fherbine/Electronic_project/TP/Altium/PCB_Project_TP/TP_Files/AssemblyDrawing.PDF

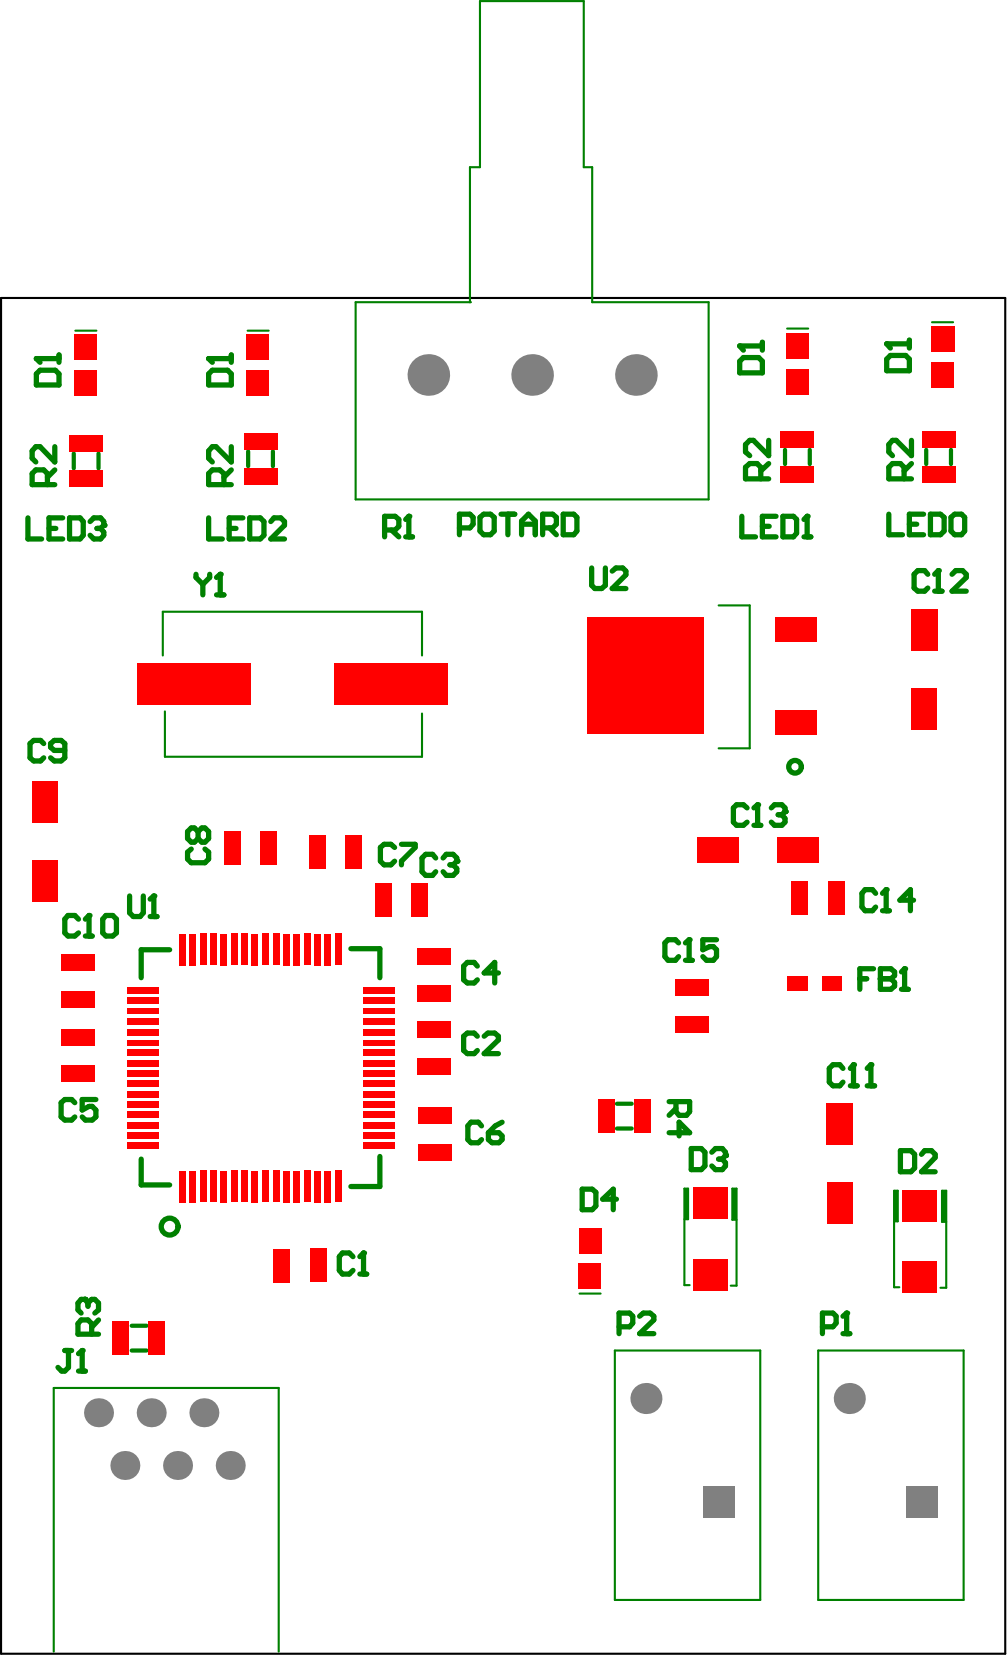
[picture p93: page 1]
