fherbine/Electronic_project/TP/Altium/PCB_Project_TP/TP_Files/MechanicalsDrawings.pdf

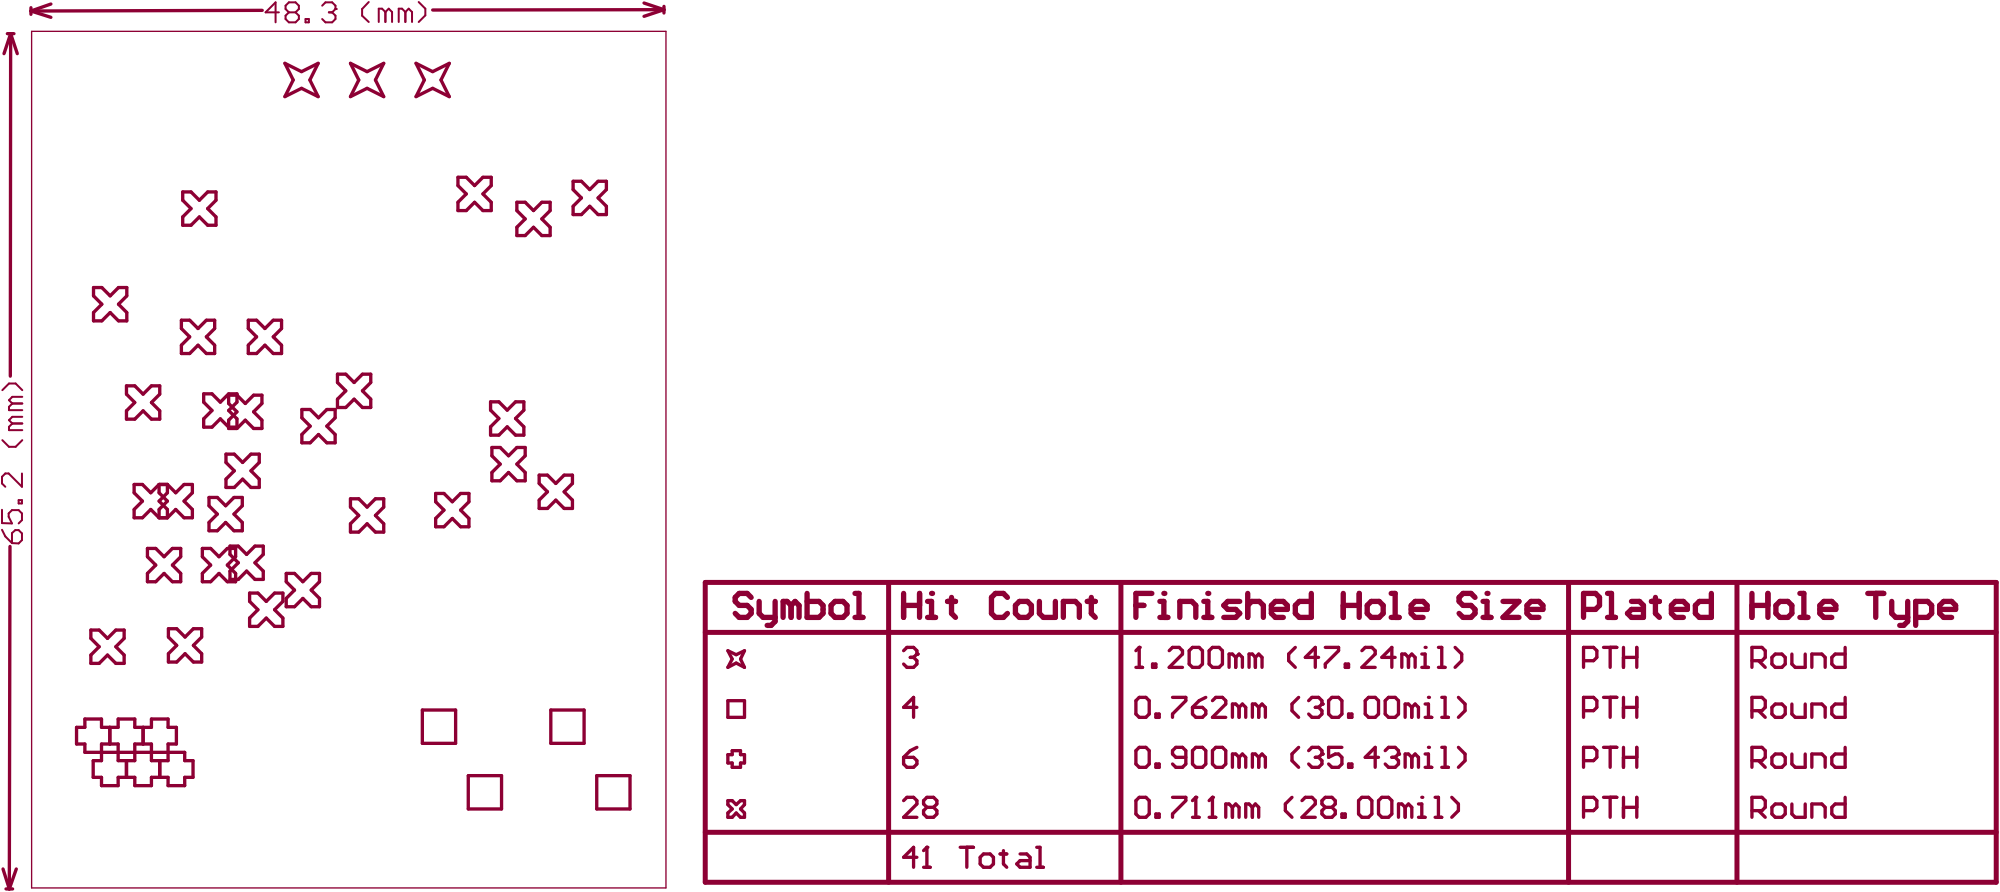
[picture p94: page 1]

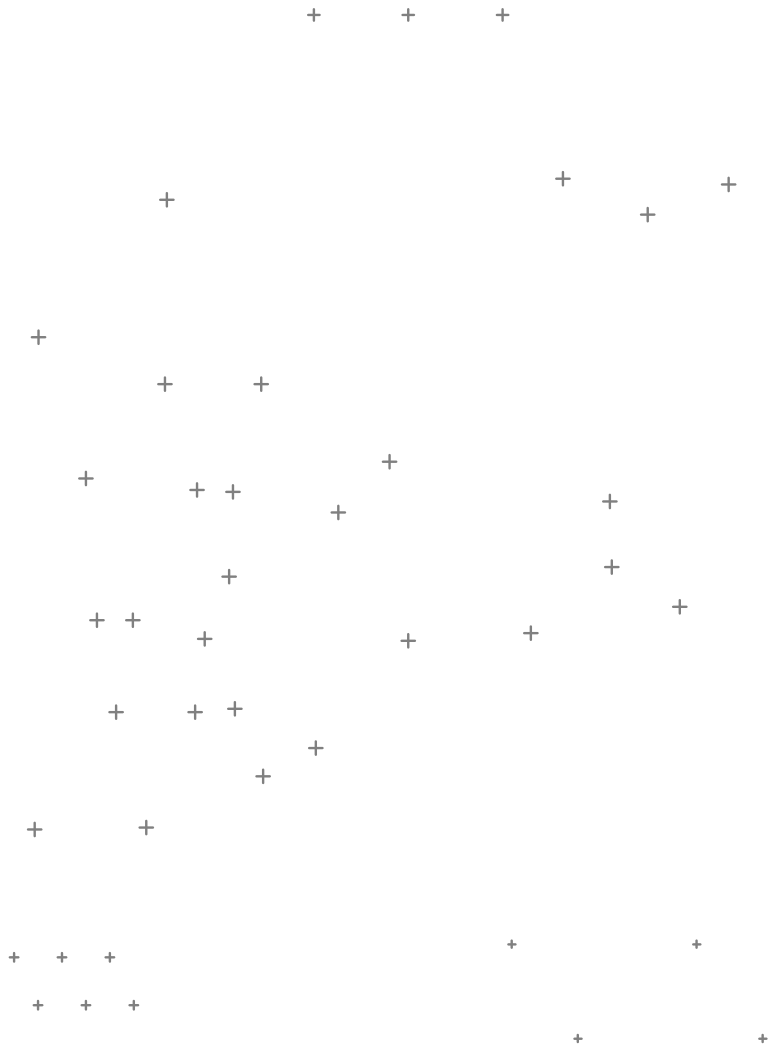
[picture p95: page 2]
