fherbine/Electronic_project/TP/Altium/PCB_Project_TP/TP_Files/Schmatics.PDF

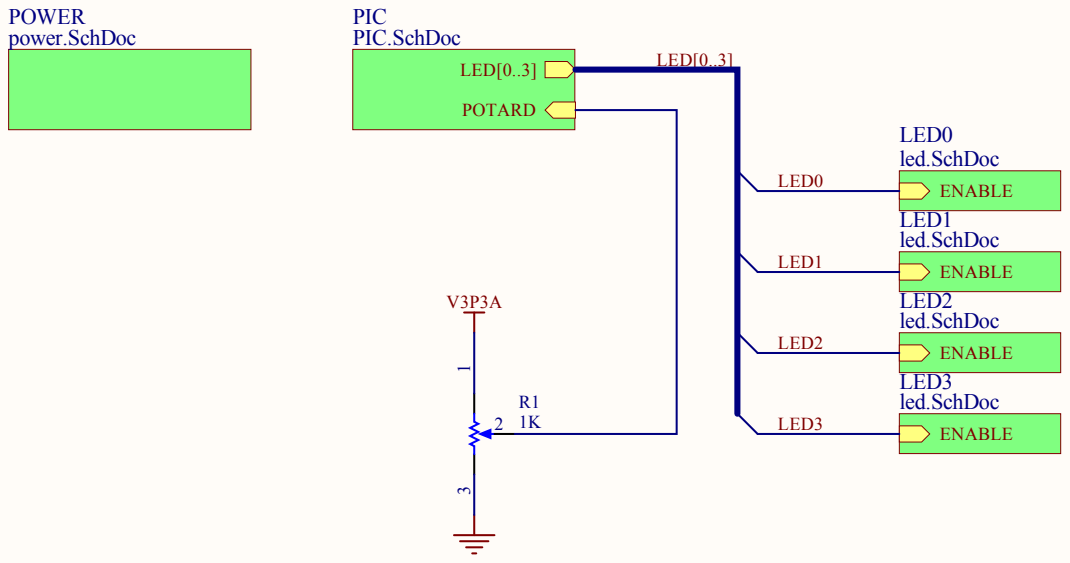
[picture p96: page 1]

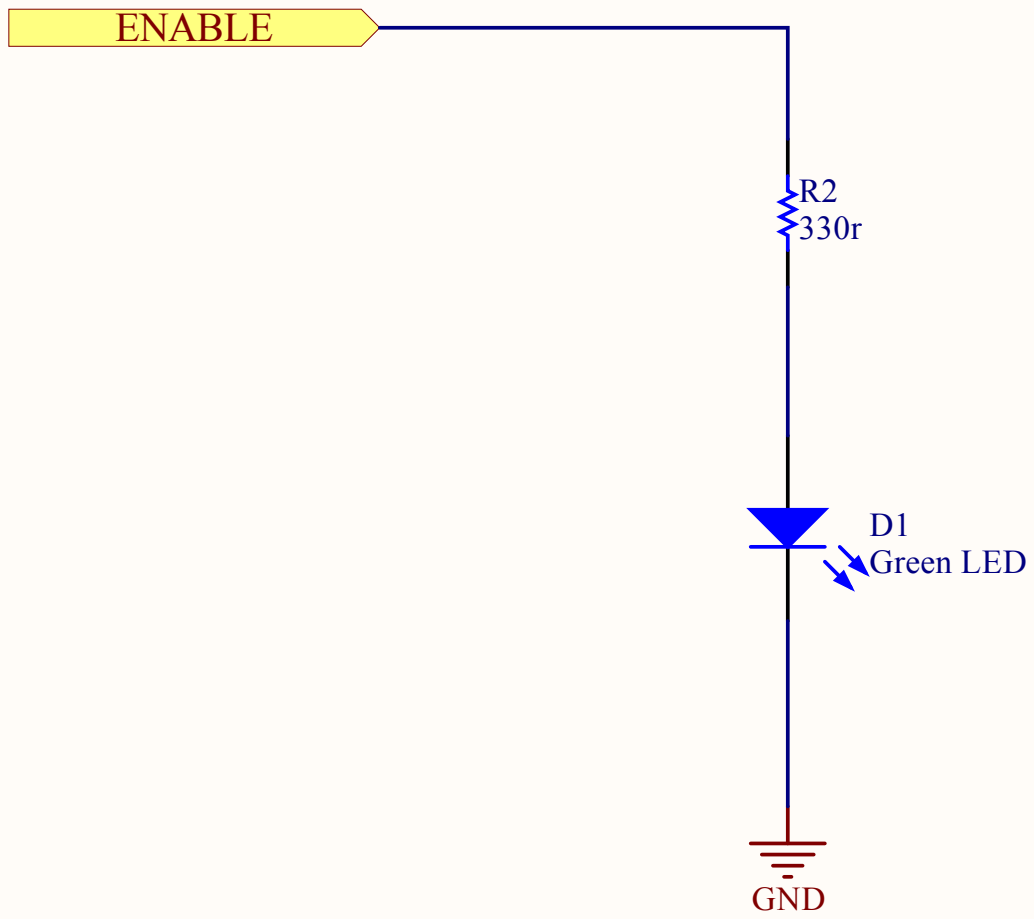
[picture p97: page 2]

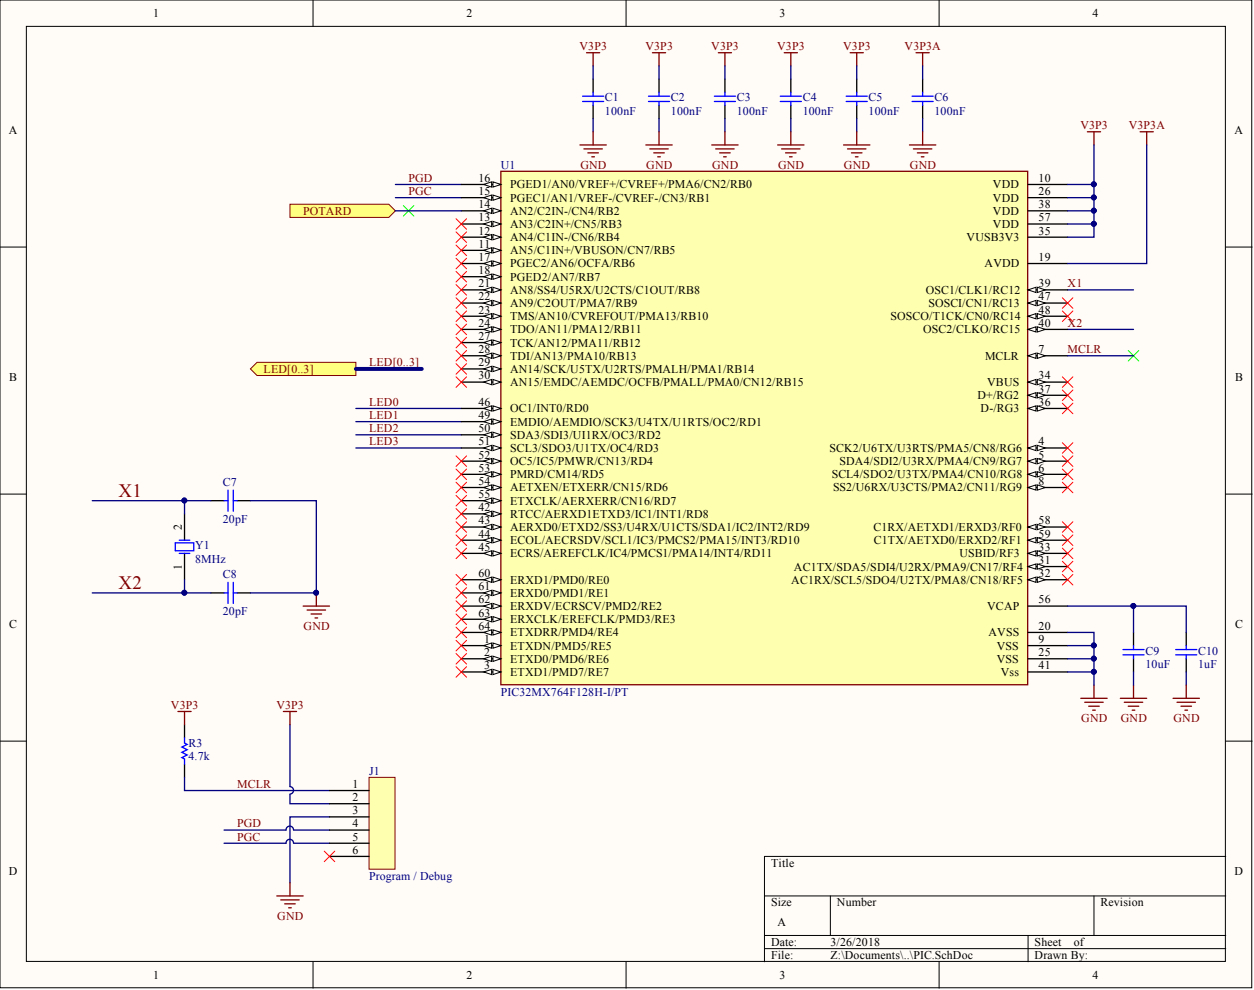
[picture p98: page 3]

2 6
3 8
5 7
3 5

2 0

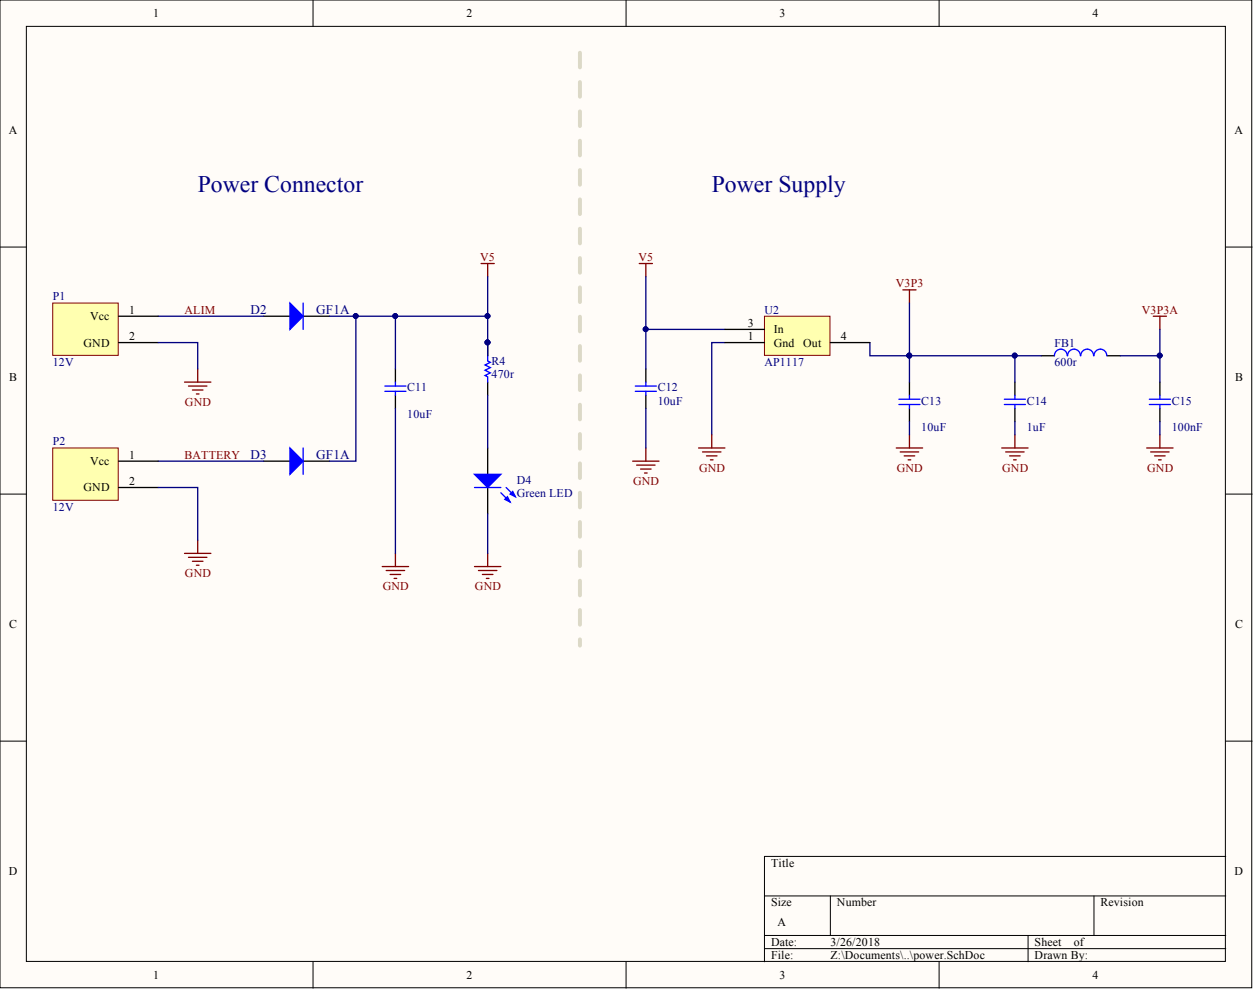
[picture p99: page 4]
