fherbine/Electronic_project/firmware/CompassIO/CompassIO_final/sources/communications.c

#include "types.h"

double parse_float(char *data, unsigned int size)
{
	long long offset = 1;
	long long floatValue = 1;
	long long result = 0;
	short neg = 1;
	int i = size;
	while (i)
	{
		if (i - 1 == 0 && data[0] == '-')
		{
			neg = -1;
			break;
		}
		if (data[i - 1] != '.' && data[i - 1] != '-')
		{
			result += (data[i - 1] - '0') * offset;
			offset *= 10;
		} else if (data[i - 1] == '.')
			floatValue = offset;
		else if (data[i - 1] < '0' && data[i - 1] > '9') // Handle wrong format
			return (999.999);
		i--;
	}
	return (((double)result/(double)floatValue) * (double)neg);
}

// lat xx.xxxxxx;long xxx.xxxxxx
u8 parser_gps_bluetooth(char *data, struct s_data *data_s)
{
	double lat = 0.0;
	double lon = 0.0;
	int separatorIndex = ft_index(data, ';');
	if (separatorIndex >= 0) {
		if (!ft_strncmp(data, "lat ", 4))
		{
			data += 4;
			lat = parse_float(data, separatorIndex - 4);
			if (lat < -90.0 || lat > 90.0) {
				//ft_putendl("Wrong latitude data");
				data_s->dest_coord.completed = FALSE;
				return (-1);
			}
			data += separatorIndex - 4 + 1; // - "lat " (4) + ";" (1)
			if (!ft_strncmp(data, "long ", 5))
			{
				data += 5;
				lon = parse_float(data, ft_strlen(data));
				if (lon < -180.0 || lon > 180.0) {
					//ft_putendl("Wrong longitude data");
					data_s->dest_coord.completed = FALSE;
					return (-1);
				}
			} else {
				data_s->dest_coord.completed = FALSE;
				return (-1);
			}
		} else {
			data_s->dest_coord.completed = FALSE;
			return (-1);
		}
	} else {
		//ft_putendl("Invalid data");
		data_s->dest_coord.completed = FALSE;
		return (-1);
	}
	data_s->dest_coord.completed = TRUE;
	data_s->dest_coord.lat = lat;
	data_s->dest_coord.lon = lon;
	//ft_putfloat(lat);
	//ft_putfloat(lon);
	data_s->store_data = TRUE;
	// Store data in flash memory												// FATAL CRASH
//	erase_sector(STORE_DEST_LAT_X1000);
//	delayms(85);
//	write_data(STORE_DEST_LAT_X1000, ((int)(lat * 1000)), 4);
//	delayms(85);
//	erase_sector(STORE_DEST_LONG_X1000);
//	delayms(85);
//	write_data(STORE_DEST_LONG_X1000, ((int)lon * 1000), 4);
//	delayms(85);
	return (0);
}
