fherbine/Electronic_project/firmware/CompassIO/CompassIO_final/sources/pps.c

#include "types.h"

void set_pps(void)
{
	ANSELA = 0;
	ANSELB = 0;
	TRISBbits.TRISB10 = 1;
	INT1Rbits.INT1R = 0b0011; // INT1 >> main button
	TRISAbits.TRISA4 = 1;
	U1RXRbits.U1RXR = 0b0010; // RX1 >> BT
	TRISBbits.TRISB1 = 1;
	U2RXRbits.U2RXR = 0b0010; // RX2 >> GPS
	TRISBbits.TRISB11 = 1;
	SDI1Rbits.SDI1R = 0b0011; // MISO1 >> FLASH

	CFGCONbits.IOLOCK = 0;
	RPB7Rbits.RPB7R = 0b0101; // OC1 >> servomotor
	RPB4Rbits.RPB4R = 0b0001; // TX1 >> BT / DEBUG 1
	RPB0Rbits.RPB0R = 0b0010; // TX2 >> GPS / DEBUG 0
	RPB13Rbits.RPB13R = 0b0011; // MOSI1 >> FLASH
	CFGCONbits.IOLOCK = 1;
}
